mats-bergstrom/DS18B20/Images/box.gif

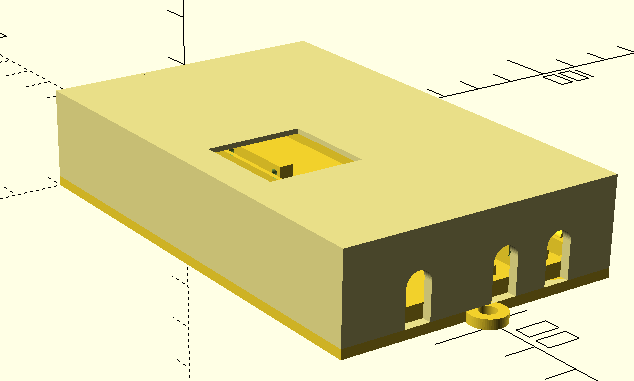
Images/box.gif
